romix123/P1-wifi-gateway/src/MQTT.h

/*
 * Copyright (c) 2022 Ronald Leenes
 *
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
 */

/**
 * @file MQTT.ino
 * @author Ronald Leenes
 * @date 28.12.2022
 *
 * @brief This file contains the MQTT functions
 *
 * @see http://esp8266thingies.nl
 */

/* MQTT part based on
 https://github.com/daniel-jong/esp8266_p1meter/blob/master/esp8266_p1meter/esp8266_p1meter.ino

*/

// **********************************
// * MQTT                           *
// **********************************

// void doMQTT(){
//   mqtt_connect();
//   if (MqttConnected) MQTT_reporter();
// }

// void mqtt_connect(){
//   if (!mqtt_client.connected()) {
//      MqttConnected = false;
//      Log.verboseln("Reconnecting to mqtt broker …");
//      mqtt_reconnect();
//   } else MqttConnected = true;
// }

// void mqtt_reconnect(){
//   if (millis() > nextMQTTreconnectAttempt) {
//     Log.verboseln("Attempting MQTT connection...");
//     statusMsg = "Attempting MQTT connection...";
//     // Create a random client ID
//     String clientId = "P1 Smart Meter – ";
//     clientId += String(random(0xffff), HEX);
//     // Attempt to connect
//     if (mqtt_client.connect(HOSTNAME, config_data.mqttUser,
//     config_data.mqttPass)){
//       Log.verboseln("   connected to broker");
//       statusMsg += "   connected to broker";
//       // Once connected, publish an announcement...
//       mqtt_client.publish("outTopic", "p1 gateway running");
//       // ... and resubscribe
//       mqtt_client.subscribe("inTopic");
//       MqttConnected = true;
//     } else {
//       Log.verbose("failed, rc=");
//       statusMsg += "failed, rc=";
//       Log.verbose(mqtt_client.state());
//       Log.verboseln(" trying again later (non blocking)");
//       statusMsg += " trying again later (non blocking)";
//       nextMQTTreconnectAttempt = millis() + 15000; // try again in 15 seconds
//       MqttConnected = false;
//     }
//   }
// }

void doMQTT() {
  bool response = mqtt_connect();
  if (response)
    MQTT_reporter();
}

bool mqtt_connect() {
  mqtt_client.setCallback(callback);
  byte i = 0;
  while (!mqtt_client.connected() && (i < 3)) {
    Log.verboseln("Attempting MQTT connection");
    // Attempt to connect
    boolean ret;

    ret = mqtt_client.connect(HOSTNAME, config_data.mqttUser,
                              config_data.mqttPass);
    if (ret) {
      Log.verboseln("Connected to MQTT");
      MqttConnected = true;
      mqtt_client.publish("outTopic", "P1 gateway");
      mqtt_client.subscribe("inTopic");
      return true;
    } else {
      MqttConnected = false;
      Log.verbose("Failed MQTT connection, return code:");

      int Status = mqtt_client.state();

      switch (Status) {
      case -4:
        Log.verboseln("Connection timeout");
        break;

      case -3:
        Log.verboseln("Connection lost");
        break;

      case -2:
        Log.verboseln("Connect failed");
        break;

      case -1:
        Log.verboseln("Disconnected");
        break;

      case 1:
        Log.verboseln("Bad protocol");
        break;

      case 2:
        Log.verboseln("Bad client ID");
        break;

      case 3:
        Log.verboseln("Unavailable");
        break;

      case 4:
        Log.verboseln("Bad credentials");
        break;

      case 5:
        Log.verboseln("Unauthorized");
        break;
      }
      if (i == 2)
        Log.verboseln("Retrying MQTT connection next cycle");
      i++;
      delay(1000);
    }
  }
  return false;
}

void callback(char *topic, byte *payload, unsigned int length) {
  Log.verbose("Message arrived [");
  Log.verbose(topic);
  Log.verbose("] ");
  for (unsigned int i = 0; i < length; i++) {
    Log.verbose("%s", (char)payload[i]);
  }
  Log.verboseln("");
}

// * Send a message to a broker topic
void send_mqtt_message(const char *topic, char *payload) {
  if (payload[0] == 0)
    return; // nothing to report
  Log.verbose("MQTT Outgoing on > ");
  Log.verbose(topic);
  Log.verbose(" > ");
  Log.verboseln(payload);
  bool result = mqtt_client.publish(topic, payload, false);

  if (!result) {
    Log.verbose("MQTT publish to topic: ");
    Log.verbose(topic);
    Log.verboseln(" failed.");
  }
}

void send_metric(String name, float metric) // added *long
{
  char value[20];
  dtostrf(metric, 3, 3, value);
  //  output ftoa(metric, output, 3);

  mtopic = String(config_data.mqttTopic) + "/" + name;
  send_mqtt_message(mtopic.c_str(), value); // output
}

void send_metric(String name, double metric) // added *long
{
  char value[20];
  dtostrf(metric, 3, 3, value);
  //  output ftoa(metric, output, 3);

  mtopic = String(config_data.mqttTopic) + "/" + name;
  send_mqtt_message(mtopic.c_str(), value); // output
}

void send_metric(String name, uint32_t metric) // added *long
{
  char value[6];
  sprintf(value, "%u", metric);
  send_mqtt_message(mtopic.c_str(), value); // output
}

void send_metric(String name, String metric) // added *long
{
  send_metric(mtopic, metric.c_str()); // output
}

void send_metric(String name, FixedValue metric) // added *long
{
  send_metric(mtopic, String(metric.val())); // output
}

void send_metric(String name, const char *metric) {
  mtopic = String(config_data.mqttTopic) + "/" + name;
  send_mqtt_message(mtopic.c_str(), (char *)metric);
}

void MQTT_reporter() {
#ifdef NEDERLANDS
  Log.verbose("MQTT reporter: ");
  Log.verboseln("%F", dsmrData.power_returned.val());
  if (mqtt_dsmr) {
    send_metric("equipmentID", dsmrData.equipment_id);

    send_metric("reading/electricity_delivered_1", dsmrData.energy_delivered_tariff1);
    send_metric("reading/electricity_delivered_2", dsmrData.energy_delivered_tariff2);
    send_metric("reading/electricity_returned_1", dsmrData.energy_returned_tariff1);
    send_metric("reading/electricity_returned_2", dsmrData.energy_returned_tariff2);
    send_metric("reading/electricity_currently_delivered", dsmrData.power_delivered);
    send_metric("reading/electricity_currently_returned", dsmrData.power_returned);

    send_metric("reading/phase_currently_delivered_l1", dsmrData.power_delivered_l1);
    send_metric("reading/phase_currently_delivered_l2", dsmrData.power_delivered_l2);
    send_metric("reading/phase_currently_delivered_l3", dsmrData.power_delivered_l3);
    send_metric("reading/phase_currently_returned_l1", dsmrData.power_returned_l1);
    send_metric("reading/phase_currently_returned_l2", dsmrData.power_returned_l2);
    send_metric("reading/phase_currently_returned_l3", dsmrData.power_returned_l3);
    send_metric("reading/phase_voltage_l1", dsmrData.voltage_l1);
    send_metric("reading/phase_voltage_l2", dsmrData.voltage_l2);
    send_metric("reading/phase_voltage_l3", dsmrData.voltage_l3);

    send_metric("consumption/gas/delivered", dsmrData.gas_delivered);

    send_metric("meter-stats/actual_tarif_group", dsmrData.electricity_tariff);
    send_metric("meter-stats/power_failure_count", dsmrData.electricity_failures);
    send_metric("meter-stats/long_power_failure_count", dsmrData.electricity_long_failures);
    send_metric("meter-stats/short_power_drops", dsmrData.electricity_sags_l1);
    send_metric("meter-stats/short_power_peaks", dsmrData.electricity_swells_l1);

    send_metric("day-consumption/electricity1",
                (dsmrData.energy_delivered_tariff1.val() - atof(log_data.dayE1)));
    send_metric("day-consumption/electricity2",
                (dsmrData.energy_delivered_tariff2.val() - atof(log_data.dayE2)));
    send_metric("day-consumption/electricity1_returned",
                (dsmrData.energy_returned_tariff1.val() - atof(log_data.dayR1)));
    send_metric("day-consumption/electricity2_returned",
                (dsmrData.energy_returned_tariff2.val() - atof(log_data.dayR2)));

    send_metric("day-consumption/electricity_merged",
                ((dsmrData.energy_delivered_tariff1.val() - atof(log_data.dayE1)) +
                 (dsmrData.energy_delivered_tariff2.val() - atof(log_data.dayE2))));
    send_metric("day-consumption/electricity_returned_merged",
                ((dsmrData.energy_returned_tariff1.val() - atof(log_data.dayR1)) +
                 (dsmrData.energy_returned_tariff2.val() - atof(log_data.dayR2))));
    send_metric("day-consumption/gas",
                (dsmrData.gas_delivered.toFloat() - atof(log_data.dayG)));

    send_metric("current-month/electricity1",
                (dsmrData.energy_delivered_tariff1.val() - atof(log_data.monthE1)));
    send_metric("current-month/electricity2",
                (dsmrData.energy_delivered_tariff2.val() - atof(log_data.monthE2)));
    send_metric("current-month/electricity1_returned",
                (dsmrData.energy_returned_tariff1.val() - atof(log_data.monthR1)));
    send_metric("current-month/electricity2_returned",
                (dsmrData.energy_returned_tariff2.val() - atof(log_data.monthR2)));

    send_metric("current-month/electricity_merged",
                ((dsmrData.energy_delivered_tariff1.val() - atof(log_data.monthE1)) +
                 (dsmrData.energy_delivered_tariff2.val() - atof(log_data.monthE2))));
    send_metric("current-month/electricity_returned_merged",
                ((dsmrData.energy_returned_tariff1.val() - atof(log_data.monthR1)) +
                 (dsmrData.energy_returned_tariff2.val() - atof(log_data.monthR2))));
    send_metric("current-month/gas",
                (dsmrData.gas_delivered.toFloat() - atof(log_data.monthG)));
  } else {
    send_metric("equipmentID", dsmrData.equipment_id);

    send_metric("consumption_low_tarif", dsmrData.energy_delivered_tariff1);
    send_metric("consumption_high_tarif", dsmrData.energy_delivered_tariff2);
    send_metric("returndelivery_low_tarif", dsmrData.energy_returned_tariff1);
    send_metric("returndelivery_high_tarif", dsmrData.energy_returned_tariff2);
    send_metric("actual_consumption", dsmrData.power_delivered);
    send_metric("actual_returndelivery", dsmrData.power_returned);

    send_metric("l1_instant_power_usage", dsmrData.power_delivered_l1);
    send_metric("l2_instant_power_usage", dsmrData.power_delivered_l2);
    send_metric("l3_instant_power_usage", dsmrData.power_delivered_l3);
    send_metric("l1_instant_power_current", dsmrData.current_l1);
    send_metric("l2_instant_power_current", dsmrData.current_l2);
    send_metric("l3_instant_power_current", dsmrData.current_l3);
    send_metric("l1_voltage", dsmrData.voltage_l1);
    send_metric("l2_voltage", dsmrData.voltage_l2);
    send_metric("l3_voltage", dsmrData.voltage_l3);
    send_metric("l1_instant_power_return", dsmrData.power_returned_l1);
    send_metric("l2_instant_power_return", dsmrData.power_returned_l2);
    send_metric("l3_instant_power_return", dsmrData.power_returned_l3);

    send_metric("gas_meter_m3", dsmrData.gas_delivered);

    send_metric("actual_tarif_group", dsmrData.electricity_tariff);
    send_metric("short_power_outages", dsmrData.electricity_failures);
    send_metric("long_power_outages", dsmrData.electricity_long_failures);
    send_metric("short_power_drops", dsmrData.electricity_sags_l1);
    send_metric("short_power_peaks", dsmrData.electricity_swells_l1);
    LastReportinMillis = millis();
    LastMReport = timestampkaal();
    MqttDelivered = true;
    return;
  }
#endif
  LastMReport = timestampkaal();
  MqttDelivered = true;
  LastReportinMillis = millis();
}

void MQTT_Debug() {
  char outstr[10];

  dtostrf(millis(), 10, 0, outstr);
  send_mqtt_message("p1wifi/P1now", outstr);

  dtostrf(nextUpdateTime, 10, 0, outstr);
  send_mqtt_message("p1wifi/P1next", outstr);

  LastMReport.toCharArray(outstr, 10);
  send_mqtt_message("p1wifi/P1time_LastMReport", outstr);

  LastTReport.toCharArray(outstr, 10);
  send_mqtt_message("p1wifi/P1time_LastTReport", outstr);

  LastJReport.toCharArray(outstr, 10);
  send_mqtt_message("p1wifi/P1time_LastJReport", outstr);

  //     dtostrf(time_to_wake, 10,0, outstr);
  //     send_mqtt_message("p1wifi/P1time_toWake", outstr);

  //    dtostrf(ESP.getFreeHeap(), 10,0, outstr);
  //     send_mqtt_message("p1wifi/P1Heap", outstr);

  //     dtostrf(ESP.getHeapFragmentation(), 10,0, outstr);
  //     send_mqtt_message("p1wifi/P1HeapFrag", outstr);

  //     dtostrf(WiFi.RSSI(), 10,0, outstr);
  //     send_mqtt_message("p1wifi/RSSI", outstr);
}
