romix123/P1-wifi-gateway/src/webserverNL.h

#ifdef NEDERLANDS

void handleSetup() {
  if (millis() > 300000) { // if we did not get here 5 mins after startup, check credentials
    Log.verboseln("indirect call");
    if (strcmp(server.arg("adminPassword").c_str(),
               config_data.adminPassword) != 0) { // passwords don't match
      Log.verboseln("Error: handlesetup entered with wrong password");
      errorLogin("Setup");
      return;
    }
  }
  Log.verboseln("direct call");
  // monitoring = false; // stop monitoring data

  String str = "";
  Log.verboseln("handleSetupForm");

  addHead(str, 0);
  addIntro(str);
  str += F("<fieldset>");
  str += F("<form action='/SetupSave' method='POST'><fieldset>");
  str += F("<input type='hidden' name='setuptoken' value='");
  str += setupToken;
  str += F("'>");
  str += F("<fieldset><legend><b>&nbsp;Admin&nbsp;</b></legend>");
  str += F("<p><b>admin password</b><br>");
  str +=
      F("<input type='text' class='form-control' name='adminPassword' value='");
  str += config_data.adminPassword;
  str += F("'></p></fieldset>");

  str += F("<fieldset><legend><b>&nbsp;Wifi parameters&nbsp;</b></legend>");
  str += F("<p><b>SSId</b><br>");
  str += F("<input type='text' class='form-control' name='ssid' value='");
  str += config_data.ssid;
  str += F("'></p>");
  str += F("<p><label><b>Password</b></label><br><input type='password' "
           "class='form-control' name='password' value='");
  str += config_data.password;
  str += F("'></p></fieldset>");

  str += F("<fieldset><legend><b>&nbsp;Domoticz parameters&nbsp;</b></legend>");

  str += F("<p><b>Rapporteer aan Domoticz?</b><input type='checkbox' "
           "class='form-control' name='domo' id='domo' ");

  if (config_data.domo[0] == 'j')
    str += F(" checked></p>");
  else
    str += F("></p>");
  str += F("<p><b>Domoticz IP address</b><input type='text' "
           "class='form-control' name='domoticzIP' value='");
  str += config_data.domoticzIP;
  str += F("'></p><p>");
  str += F("<b>Domoticz Port</b><input type='text' class='form-control' "
           "name='domoticzPort' value='");
  str += config_data.domoticzPort;
  str += F("'></p><p>");
  str += F("<b>Domoticz Gas Idx</b><input type='text' class='form-control' "
           "name='domoticzGasIdx' value='");
  str += config_data.domoticzGasIdx;
  str += F("'></p><p>");
  str += F("<b>Domoticz Energy Idx</b><input type='text' class='form-control' "
           "name='domoticzEnergyIdx' value='");
  str += config_data.domoticzEnergyIdx;
  str += F("'></p>");
  str += F("</fieldset>");

  str += F("<fieldset><legend><b>&nbsp;MQTT parameters&nbsp;</b></legend>");
  str += F("<p><b>Rapporteer aan MQTT broker?</b><input type='checkbox' "
           "class='form-control' name='mqtt' id='mqtt' ");
  if (config_data.mqtt[0] == 'j')
    str += F(" checked></p>");
  else
    str += F("></p>");
  str += F("<p><b>MQTT broker IP address</b><input type='text' "
           "class='form-control' name='mqttIP' value='");
  str += config_data.mqttIP;
  str += F("'></p><p>");
  str += F("<b>MQTT broker Port</b><input type='text' class='form-control' "
           "name='mqttPort' value='");
  str += config_data.mqttPort;
  str += F("'></p><p>");
  str += F("<b>MQTT user</b><input type='text' class='form-control' "
           "name='mqttUser' value='");
  str += config_data.mqttUser;
  str += F("'></p><p>");
  str += F("<b>MQTT password</b><input type='text' class='form-control' "
           "name='mqttPass' value='");
  str += config_data.mqttPass;
  str += F("'></p>");
  str += F("<b>MQTT root topic</b><input type='text' class='form-control' "
           "name='mqttTopic' value='");
  str += config_data.mqttTopic;
  str += F("'></p>");
  str += F("</fieldset>");
  str += F("<fieldset>");
  str += F("<b>Meetinterval in sec (> 10 sec)</b><input type='text' "
           "class='form-control' name='interval' value='");
  str += config_data.interval;
  str += F("'></p><p>");
  str += F("<p><b>Rapporteer in watt (ipv van in kWh) </b><input "
           "type='checkbox' class='form-control' name='watt' id='watt' ");
  if (config_data.watt[0] == 'j')
    str += F(" checked></p>");
  else
    str += F("></p>");
  str += F("<p><b>Activeer Telnet poort (23) </b><input type='checkbox' "
           "class='form-control' name='telnet' id='telnet' ");
  if (config_data.telnet[0] == 'j')
    str += F(" checked></p>");
  else
    str += F("></p>");
  str += F("<p><b>Debug via MQTT </b><input type='checkbox' "
           "class='form-control' name='debug' id='debug' ");
  if (config_data.debug[0] == 'j')
    str += F(" checked></p>");
  else
    str += F("></p>");
  str += F("</fieldset><div></div>");
  str += F("<p><button type='submit'>Save</button></form>");
  str += F("<form action='/' method='POST'><button class='button "
           "bhome'>Menu</button></form></p>");
  addFoot(str);
  server.send(200, "text/html", str);
}

void handleP1() {
  Log.verbose("handleP1: actualElectricityPowerRet: ");
  Log.verboseln("%F", dsmrData.power_returned.val());
  Log.verbose("handleP1: actualElectricityPowerDeli: ");
  Log.verboseln("%F", dsmrData.power_delivered.val());
  Log.verboseln("handleP1");
  String str = "";
  String eenheid, eenheid2, eenheid3;
  if (reportInDecimals)
    eenheid = " kWh'></div>";
  else
    eenheid = " Wh'></div>";
  // if (reportInDecimals) eenheid = " kWh</div></div>"; else eenheid = "
  // Wh</div></div>";
  if (reportInDecimals)
    eenheid2 = " kW'></div></p>";
  else
    eenheid2 = " W'></div></p>";

  addHead(str, 60);
  addIntro(str);

  str += F("<form ><fieldset><legend><b>Meetwaarden</b></legend>");

  str += "<p><div class='row'><div class='column'><b>Verbruik laag tarief: "
         "totaal</b><input type='text' class='form-control c6' value='";
  str += String(dsmrData.energy_delivered_tariff1);
  str += eenheid;
  str += "<div class='column' style='text-align:right'><b>vandaag</b><input "
         "type='text' class='form-control c7' value='";
  str += dsmrData.energy_delivered_tariff1.val() - atof(log_data.dayE1);
  str += eenheid;
  str += "</div></p>";

  str += "<p><div class='row'><div class='column'><b>Verbruik hoog tarief: "
         "totaal</b><input type='text' class='form-control c6' value='";
  str += String(dsmrData.energy_delivered_tariff2);
  str += eenheid;
  str += "<div class='column' style='text-align:right'><b>vandaag</b><input "
         "type='text' class='form-control c7' value='";
  str += dsmrData.energy_delivered_tariff2.val() - atof(log_data.dayE2);
  str += eenheid;
  str += "</div></p>";

  str += "<p><div class='row'><div class='column'><b>Retour laag tarief: "
         "totaal</b><input type='text' class='form-control c6' value='";
  str += String(dsmrData.energy_returned_tariff1);
  str += eenheid;
  str += "<div class='column' style='text-align:right'><b>vandaag</b><input "
         "type='text' class='form-control c7' value='";
  str += dsmrData.energy_returned_tariff1.val() - atof(log_data.dayR1);
  str += eenheid;
  str += "</div></p>";

  str += "<p><div class='row'><div class='column'><b>Retour hoog tarief: "
         "totaal</b><input type='text' class='form-control c6' value='";
  str += String(dsmrData.energy_returned_tariff2);
  str += eenheid;
  str += "<div class='column' style='text-align:right'><b>vandaag</b><input "
         "type='text' class='form-control c7' value='";
  str += dsmrData.energy_returned_tariff2.val() - atof(log_data.dayR2);
  str += eenheid;
  str += "</div></p>";

  Log.verbose("buildpage: actualElectricityPowerRet: ");
  Log.verboseln("%F", dsmrData.power_returned.val());
  Log.verbose("handleP1: actualElectricityPowerDeli: ");
  Log.verboseln("%F", dsmrData.power_delivered.val());

  str += "<p><div class='row'><b>Actueel verbruik</b><input type='text' "
         "class='form-control c6' value='";
  str += String(dsmrData.power_delivered.val());
  str += eenheid2;

  str += "<p><div class='row'><b>Actueel retour</b><input type='text' "
         "class='form-control c6' value='";
  str += String(dsmrData.power_returned.val());;
  str += eenheid2;

  if (dsmrData.P1prot() == 5) {
    str += "<p><div class='row'><div class='column3'><b>Voltage: L1</b><input "
           "type='text' class='form-control c6' value='";
    str += String(dsmrData.voltage_l1.val());
    str += " V'></div>";
    str += "<div class='column3' style='text-align:right'><b>L2</b><input "
           "type='text' class='form-control c7' value='";
    str += String(dsmrData.voltage_l2.val());
    str += " V'></div>";
    str += "<div class='column3' style='text-align:right'><b>L3</b><input "
           "type='text' class='form-control c7' value='";
    str += String(dsmrData.voltage_l3.val());
    str += " V'></div></div></p>";

    str += "<p><div class='row'><div class='column3'><b>Verbruik: L1</b><input "
           "type='text' class='form-control c6' value='";
    str += String(dsmrData.power_delivered_l1.val());
    str += " kW'></div>";
    str += "<div class='column3' style='text-align:right'><b>L2</b><input "
           "type='text' class='form-control c7' value='";
    str += String(dsmrData.power_delivered_l2.val());
    str += " kW'></div>";
    str += "<div class='column3' style='text-align:right'><b>L3</b><input "
           "type='text' class='form-control c7' value='";
    str += String(dsmrData.power_delivered_l3.val());
    str += " kW'></div></div></p>";

    str += "<p><div class='row'><div class='column3'><b>Retour: L1</b><input "
           "type='text' class='form-control c6' value='";
    str += String(dsmrData.power_returned_l1.val());
    str += " kW'></div>";
    str += "<div class='column3' style='text-align:right'><b>L2</b><input "
           "type='text' class='form-control c7' value='";
    str += String(dsmrData.power_returned_l2.val());
    str += " kW'></div>";
    str += "<div class='column3' style='text-align:right'><b>L3</b><input "
           "type='text' class='form-control c7' value='";
    str += String(dsmrData.power_returned_l3.val());
    str += " kW'></div></div></p>";
  }
  str += "<p><div class='row'><div class='column3'><b>Amperage: L1</b><input "
         "type='text' class='form-control c6' value='";
  str += String(dsmrData.current_l1.val());
  str += " A'></div>";
  str += "<div class='column3' style='text-align:right'><b>L2</b><input "
         "type='text' class='form-control c7' value='";
  str += String(dsmrData.current_l2.val());
  str += " A'></div>";
  str += "<div class='column3' style='text-align:right'><b>L3</b><input "
         "type='text' class='form-control c7' value='";
  str += String(dsmrData.current_l3.val());
  str += " A'></div></div></p>";
  /*

    str += F("<p><b>Voltage dips</b><input type='text' class='form-control'
    style='text-align:right' value='"); str += numberVoltageSagsL1; str +=
    F("'></p>"); str += F("<p><b>Voltage pieken</b><input type='text'
    class='form-control' style='text-align:right' value='"); str +=
    numberVoltageSwellsL1; str += F("'></p>"); str +=
    F("<p><b>Stroomonderbrekingen</b><input type='text' class='form-control'
    style='text-align:right' value='"); str += numberPowerFailuresAny; str +=
    F("'></p>");
    */
  str += "<p><div class='row'><div class='column'><b>Gasverbruik: "
         "totaal</b><input type='text' class='form-control c6' value='";
  str += dsmrData.gas_delivered;
  str += F(" m3'></div>");
  str += "<div class='column' style='text-align:right'><b>vandaag</b><input "
         "type='text' class='form-control c7' value='";
  str += dsmrData.gas_delivered.toFloat() - atof(log_data.dayG);
  str += " m3'></div></div></p>";
  str += F("</fieldset></form>");
  str += F("<form action='/' method='POST'><button class='button "
           "bhome'>Menu</button></form>");
  addUptime(str);
  addFoot(str);
  server.send(200, "text/html", str);
}

void handleRawData() {
  String str;
  Log.verboseln("Raw data requested. Here you go.");
  str = "<html><head></head><body>";
  str += datagram;
  str += "</body></html>";
  if (dataEnd) {
    server.send(200, "text/html", str);
    Log.verbose("%s\n", datagram);
  }
}

#endif
