romix123/P1-wifi-gateway/src/graph.h

/*
 * Copyright (c) 2022 Ronald Leenes
 *
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



 * @file graph.ino
 * @author Ronald Leenes

 *
 * @brief This file contains the graphing functions
 *
 * @see http://esp8266thingies.nl
 */

#if GRAPH == 1

void handleGraphMenu() {
  String str = "";

  addHead(str, 0);
  addIntro(str);

  str += F("<fieldset><legend><b> Grafieken </b></legend>");
  str += F("<fieldset><legend><b> periode </b></legend>");
  str += F("<form action='/SelectGraph' method='POST'>");
  str += F("<div ><table width='95%' ><tr>");
  str += F("<td width='25%'><input type='radio' id='day' name='period' "
           "value='day' checked /><label for='day'>vandaag</label></td>");
  str += F("<td width='25%'><input type='radio' id='week' name='period' "
           "value='week' /><label for='week'>deze week</label></td>");
  str += F("<td width='25%'><input type='radio' id='month' name='period' "
           "value='month' /><label for='month'>deze maand</label></td>");
  str += F("<td width='25%'><input type='radio' id='year' name='period' "
           "value='year' /><label for='year'>dit "
           "jaar</label></td></tr></table></br>");
  str += F("</div>");

  //  str += F("<fieldset>");
  str += F("<button name='graphtype' value='1' type='submit'>Energieverbruik "
           "T1/T2</button>");
  str += F("<p><button name='graphtype' value='2' type='submit'>Energie retour "
           "T1/T2</button>");
  str += F("<p><button name='graphtype' value='3' type='submit'>Energie "
           "totaal/retour</button>");
  str += F("<p><button name='graphtype' value='4' "
           "type='submit'>Gasverbruik</button>");
  str += F("</form>");
  str += F("</fieldset>");

  str += F("<fieldset><legend><b> Jaaroverzicht</b></legend>");
  str += F("<form action='/GasCalendar' method='POST'>");
  str += F("<p><button type='submit'>Gasverbruik dit jaar</button></form>");
  str += F("</fieldset></form>");

  str += F("</fieldset>"); // grafieken
  //  str += F("<form action='/Dir' method='GET'><button
  //  type='submit'>Directory</button></form>");
  str += F("<form action='/' method='POST'><button class='button "
           "bhome'>Menu</button>");

  addFootBare(str);
  server.send(200, "text/html", str);
}

void DumpDataFiles() {
  listDir("/");
  Log.verboseln("");
}

void selectGraph() {
  char switcher[3];
  strncpy(switcher, server.arg("graphtype").c_str(),
          server.arg("graphtype").length());
  switcher[1] = '\0';

  char period[6];
  strncpy(period, server.arg("period").c_str(), server.arg("period").length());
  period[server.arg("period").length()] = '\0';

  Log.verbose("Selected graph: ");
  Log.verboseln(switcher);
  Log.verbose("Selected period: ");
  Log.verboseln(period);

  if (server.method() == HTTP_POST) {
    //  int switcher = atoi(server.arg("datatype").c_str());
    Log.verboseln(switcher);
    switch (atoi(switcher)) {
    case 1: // delivered T1/T2
      //     theGraph("E1.log", "E2.log", "Elektriciteit gebruik T1",
      //     "Elektriciteit gebruik T2", "[{label:'uur',
      //     type:'number'},{label:'kWh', type:'number'}],", period );
      theGraph("E1", "E2", "Elektriciteit gebruik T1",
               "Elektriciteit gebruik T2",
               "[{label:'uur', type:'number'},{label:'kWh', type:'number'}],",
               period);
      break;
    case 2: // returned T1/T2
            //    theGraph("R1.log", "R2.log","Elektriciteit retour T1",
            //    "Elektriciteit retour T2", "[{label:'uur',
            //    type:'number'},{label:'kWh', type:'number'}],", period);
      theGraph("R1", "R2", "Elektriciteit retour T1", "Elektriciteit retour T2",
               "[{label:'uur', type:'number'},{label:'kWh', type:'number'}],",
               period);
      break;
    case 3: // Total E
      //      theGraph("TE.log", "TR.log", "Elektriciteit totaal gebruik",
      //      "Elektriciteit totaal retour", "[{label:'uur',
      //      type:'number'},{label:'kWh', type:'number'}],", period);
      theGraph("TE", "TR", "Elektriciteit totaal gebruik",
               "Elektriciteit totaal retour",
               "[{label:'uur', type:'number'},{label:'kWh', type:'number'}],",
               period);
      break;
    case 4: // Gas
      //      theGraph("G.log", "","Gas","", "[{label:'uur',
      //      type:'number'},{label:'kubieke meter', type:'number'}],", period);
      theGraph("G", "", "Gas", "",
               "[{label:'uur', type:'number'},{label:'kubieke meter', "
               "type:'number'}],",
               period);
      break;
    default:
      break;
    }
  }
}

void theGraph(const char *type1, const char *type2, String title1,
              String title2, String label, String period) {
  monitoring = false;
  String str = "";
  char buffer[64];
  char path1[20];
  char path2[20];
  String pageTitle = "";

  if (period == "day") {
    strcpy(path1, "/Hour");
    strcat(path1, type1);
    strcpy(path2, "/Hour");
    strcat(path2, type2);
    pageTitle = " Vandaag ";
  } else if (period == "week") {
    strcpy(path1, "/Week");
    strcat(path1, type1);
    strcpy(path2, "/Week");
    strcat(path2, type2);
    pageTitle = " Deze week ";
  } else if (period == "month") {
    strcpy(path1, "/Month");
    strcat(path1, type1);
    strcpy(path2, "/Month");
    strcat(path2, type2);
    pageTitle = " Deze maand ";

  } else if (period == "year") {
    strcpy(path1, "/Year");
    strcat(path1, type1);
    strcpy(path2, "/Year");
    strcat(path2, type2);
    pageTitle = " Dit jaar ";
  }
  strcat(path1, ".log");
  strcat(path2, ".log");

  /*
  const char* measures[] = {"E1", "E2", "R1", "R2", "TE", "TR", "G"};
  const char* offsets[] = {"hour", "day", "week", "month", "year"};
  int *target1, *target2;
  int measure1, measure2;
  char startval1[12], startval2[12];

  int offset =0;
    for (int i = 0; i < 6; i++) {
      if (String(type1) == measures[i]) {
        measure1 = i;
        break;
      }
    }
    for (int i = 0; i < 6; i++) {
      if (String(type2) == measures[i]) {
        measure2 = i;
        break;
      }
    } // we no know which datum we need to retrieve from log_data, now we have
  to find the correct offset (period) for (int i = 0; i < 6; i++) { if (period
  == offsets[i]) { offset = i; break;
      }
    }
    // we now have pointers to direct us to the correct location in the log_data
  struct to retrieve the beginning of period value
    //each period uses 7 * 12 bytes

  target1 = (int*)&log_data + offset * 84 + measure1 * 12; //
  Log.verbose("Target 1: ");
  Log.verboseln(offset * 84 + measure1 * 12);
   for (int i = 0; i < 12; i++) {
    startval1[i] = *(target1);
    target1++;
   }
   Log.verbose("value :");
   Log.verboseln(startval1);
  //target2 = (int*)&log_data + offset * 84 + measure2 * 12; //

   int *p;
    // take address of displayDefault and assign to the pointer
    p = (int*)&displayDefault;

    // loop thorugh the elements of the struct
    for (uint8_t cnt = 0; cnt < sizeof(displayDefault) / sizeof(int); cnt++)
    {
      // p points to an address of an element in the array; *p gets you the
  value ofthat address
      // print it and next point the pointer to the address of the next element
      Log.verboseln(*(p++));
    }

    int *p;
    p = (int*)&log_data;

  */
  // Log.verbose("file1 to read: ");
  // Log.verboseln(path1);
  // Log.verbose("file2 to read: ");
  // Log.verboseln(path2);

  // https://stackoverflow.com/questions/44159990/how-to-add-a-total-to-a-chart-in-google-charts

  File file1 = FST.open(path1, "r");
  File file2 = FST.open(path2, "r");

  addGraphHead(str);
  str += F("<script type=\"text/javascript\" "
           "src=\"https://www.gstatic.com/charts/loader.js\"></script>");
  str += F("<script type=\"text/javascript\">google.charts.load('current', "
           "{'packages':['corechart']});");
  str += F("google.charts.setOnLoadCallback(drawChart1);");
  if (type2[0] != '\0') {
    str += F("google.charts.setOnLoadCallback(drawChart2);");
  }

  server.sendContent(str);
  // Log.verboseln(str);

  // str += F("function getSum(data, column){var total = 0;for (i = 0; i <
  // data.getNumberOfRows(); i++) total = total + data.getValue(i, column);
  // return total;}");

  str = F("function drawChart1() { var data = new "
          "google.visualization.arrayToDataTable([");
  str += label; // F("[\"uur\", \"m^3\"], ");
  server.sendContent(str);
  // Log.verboseln(str);

  if (!file1) {
    Log.verboseln("Failed to open file for reading");
    server.sendContent("['0', 0],");
    //    Log.verbose("['0', 0], ");
  } else {
    while (file1.available()) {
      int l = file1.readBytesUntil('\n', buffer, sizeof(buffer));
      buffer[l] = 0;
      server.sendContent(buffer);
      //     Log.verboseln(buffer);
    }
    file1.close();
  }
  delay(200);
  str = F("]);");
  str += F("var options = {title: '");
  str += title1;
  str += F(" '};"); //'Gasverbruik per uur in m^3'};");
  if (type1[0] == 'T')
    str +=
        F("var chart = new "
          "google.visualization.LineChart(document.getElementById('Chart1'));");
  else
    str += F(
        "var chart = new "
        "google.visualization.ColumnChart(document.getElementById('Chart1'));");
  str += F("chart.draw(data, options); }");
  server.sendContent(str);
  // Log.verboseln(str);
  delay(200);

  str = "";

  if (type2[0] != '\0') {
    str = F("function drawChart2() { var data = new "
            "google.visualization.arrayToDataTable([");
    str += label; // F("[\"uur\", \"m^3\"], ");
    server.sendContent(str);
    //  Log.verboseln(str);

    if (!file2) {
      Log.verboseln("Failed to open file for reading");
      server.sendContent("['0', 0],");
      Log.verbose("['0', 0], ");
    } else {
      while (file2.available()) {
        int l = file2.readBytesUntil('\n', buffer, sizeof(buffer));
        buffer[l] = 0;
        server.sendContent(buffer);
        Log.verbose("%s", str);
      }
      file2.close();
      delay(200);
    }
    str = F("]);");
    str += F("var options = {title: '");
    str += title2; //'Gasverbruik per uur in m^3'
    str += F(" '};");
    if (type2[0] == 'T')
      str += F(
          "var chart = new "
          "google.visualization.LineChart(document.getElementById('Chart2'));");
    else
      str += F("var chart = new "
               "google.visualization.ColumnChart(document.getElementById('"
               "Chart2'));");
    str += F("chart.draw(data, options); }");
    server.sendContent(str);
    //  Log.verboseln(str);
  } // only if we have a second file to display

  str = F("</script>");
  str += F("</head><body>");
  str += ("<div "
          "style='text-align:left;display:inline-block;color:#000000;width:"
          "600px;'><div style='text-align:center;color:#000000;'><h2>P1 "
          "wifi-gateway</h2></div><br>");

  str += F("<fieldset><legend><b>");
  str += pageTitle;
  str += F("</b></legend>");
  str += F("<div id='Chart1' style='width:100%; max-width:1200px; "
           "height:500px'></div><br>");
  str += F("Totaal deze periode: ");
  str += totalXY(type1, period);
  if (type2[0] != '\0') {
    str += F("<div id=\"Chart2\" style=\"width:100%; max-width:1200px; "
             "height:500px\"></div><br>");
    str += F("Totaal deze periode: ");
    str += totalXY(type2, period);
    str += "</br></fieldset>";
  }
  str += F("<form action='/' method='POST'><button class='button "
           "bhome'>Menu</button></form>");
  addFootBare(str);
  server.sendContent(str);
  //  Log.verboseln(str);
  server.sendContent(F(""));
  monitoring = true;
}

void calendarGas() {
  String str = "";
  char buffer[64];
  File file = FST.open("/YearGc.log", "r");
  monitoring = false;

  addGraphHead(str);

  str +=
      F("<script type='text/javascript' "
        "src='https://www.gstatic.com/charts/loader.js'></script><script "
        "type='text/javascript'>google.charts.load('current', "
        "{packages:['calendar']});google.charts.setOnLoadCallback(drawChart);");
  str += F(
      "function drawChart() {var dataTable=new "
      "google.visualization.DataTable(); dataTable.addColumn({ type: 'date', "
      "id: 'Datum' }); dataTable.addColumn({type: 'number', id: 'Gebruik'});");
  str += F("dataTable.addRows([");

  server.sendContent(str);
  // Log.verboseln(str);

  if (!file) {
    Log.verboseln("Failed to open file for reading");
    server.sendContent("[new Date(2023,0,1), 0],");
  } else {
    while (file.available()) {
      int l = file.readBytesUntil('\n', buffer, sizeof(buffer));
      buffer[l] = 0;
      server.sendContent("[new Date");
      server.sendContent(buffer);
    }
    file.close();
    delay(200);
  }
  str = "";
  str +=
      F("]); var chart = new "
        "google.visualization.Calendar(document.getElementById('calendar_gas'))"
        "; var options = { title: 'Gas gebruiksintensiteit', height: 350};");
  str += F(
      "chart.draw(dataTable, options);}</script></head><body><div "
      "id='calendar_gas' style='width: 800px; height: 350px;'></div><div><form "
      "action='/' method='POST'><button class='button bhome' style='width: "
      "300px' >Menu</button></form></div>");

  addFootBare(str);
  server.sendContent(str);
  // Log.verboseln(str);
  server.sendContent(F(""));

  monitoring = true;
}

#endif // GRAPH
