romix123/P1-wifi-gateway/src/CRC32.cpp

#include <stdint.h>
#include <stdio.h>

// the CRC routine
uint32_t calculateCRC32(const uint8_t *data, size_t length) {
  uint32_t crc = 0xffffffff;
  while (length--) {
    uint8_t c = *data++;
    for (uint32_t i = 0x80; i > 0; i >>= 1) {
      bool bit = crc & 0x80000000;
      if (c & i) {
        bit = !bit;
      }

      crc <<= 1;
      if (bit) {
        crc ^= 0x04c11db7;
      }
    }
  }

  return crc;
}
