romix123/P1-wifi-gateway/src/p1debug.h

/*
 * Copyright (c) 2022 Ronald Leenes
 *
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
 */

/**
 * @file debug.ino
 * @author Ronald Leenes
 * @date 28.12.2022
 *
 * @brief This file contains debug functions
 *
 * @see http://esp8266thingies.nl
 */

void readVoltage() { // read internal VCC
  volts = ESP.getVcc();
  Log.verbose("The internal VCC reads %1.2f volts\n", volts / 1000);
}

void PrintConfigData() {
  Log.verbose("dataSet : ");
  Log.verboseln(config_data.dataSet);
  Log.verbose("Admin password : ");
  Log.verboseln(config_data.adminPassword);
  Log.verbose("SSID : ");
  Log.verboseln(config_data.ssid);
  Log.verbose("password : ");
  Log.verboseln(config_data.password);
  Log.verbose("DomoticxIP : ");
  Log.verboseln(config_data.domoticzIP);
  Log.verbose("DomoticzPort : ");
  Log.verboseln(config_data.domoticzPort);
  Log.verbose("domotixzGasIdx : ");
  Log.verboseln(config_data.domoticzGasIdx);
  Log.verbose("domotixzEnergyIdx : ");
  Log.verboseln(config_data.domoticzEnergyIdx);

  Log.verbose("mqttIP : ");
  Log.verboseln(config_data.mqttIP);
  Log.verbose("mqttPort : ");
  Log.verboseln(config_data.mqttPort);
  Log.verbose("mqttUser : ");
  Log.verboseln(config_data.mqttUser);
  Log.verbose("mqttPass : ");
  Log.verboseln(config_data.mqttPass);
  Log.verbose("mqttTopic : ");
  Log.verboseln(config_data.mqttTopic);

  Log.verbose("interval : ");
  Log.verboseln(config_data.interval);
  Log.verbose("json : ");
  Log.verboseln(config_data.domo);
  Log.verbose("mqtt : ");
  Log.verboseln(config_data.mqtt);
  Log.verbose("watt : ");
  Log.verboseln(config_data.watt);
  Log.verbose("telnet : ");
  Log.verboseln(config_data.telnet);
}
